Luchangling/WirelessGPSTracker/doc/亮灯规则.jpg

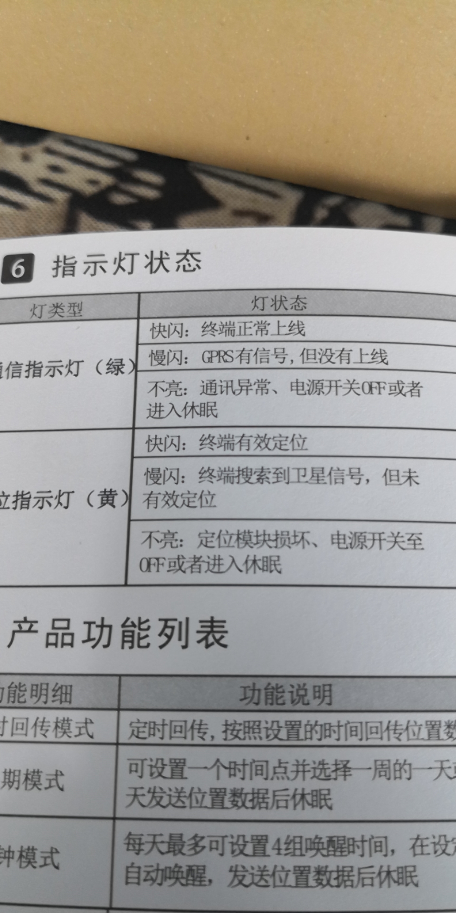
doc/亮灯规则.jpg
