Luchangling/WirelessGPSTracker/mcu/Bsp/src/stm8l15x_it.c

/**
  ******************************************************************************
  * @file    TIM2/TIM2_TRIGLSE/stm8l15x_it.c
  * @author  MCD Application Team
  * @version V1.5.2
  * @date    30-September-2014
  * @brief   Main Interrupt Service Routines.
  *          This file provides template for all peripherals interrupt service routine.
  ******************************************************************************
  * @attention
  *
  * <h2><center>&copy; COPYRIGHT 2014 STMicroelectronics</center></h2>
  *
  * Licensed under MCD-ST Liberty SW License Agreement V2, (the "License");
  * You may not use this file except in compliance with the License.
  * You may obtain a copy of the License at:
  *
  *        http://www.st.com/software_license_agreement_liberty_v2
  *
  * Unless required by applicable law or agreed to in writing, software 
  * distributed under the License is distributed on an "AS IS" BASIS, 
  * WITHOUT WARRANTIES OR CONDITIONS OF ANY KIND, either express or implied.
  * See the License for the specific language governing permissions and
  * limitations under the License.
  *
  ******************************************************************************
  */ 

/* Includes ------------------------------------------------------------------*/
#include "stm8l15x_it.h"
#include "app_ticks_timer.h"
#include "stm8l15x_rtc.h"
#include "main.h"
#include "bsp_comm_uart.h"
#include "bsp_light_sensor.h"
#include "app.h"
#include "bsp.h"
#include "feature_config.h"

/** @addtogroup STM8L15x_StdPeriph_Examples
  * @{
  */

/** @addtogroup TIM2_TRIGLSE
  * @{
  */
/* Private typedef -----------------------------------------------------------*/
/* Private define ------------------------------------------------------------*/
/* Private macro -------------------------------------------------------------*/
/* Private variables ---------------------------------------------------------*/
/* Private function prototypes -----------------------------------------------*/
/* Private functions ---------------------------------------------------------*/
/* Public functions ----------------------------------------------------------*/
static u16 s_exti1 = 0;
#ifdef _COSMIC_
/**
  * @brief Dummy interrupt routine
  * @param  None
  * @retval None
  */
INTERRUPT_HANDLER(NonHandledInterrupt, 0)
{
  /* In order to detect unexpected events during development,
     it is recommended to set a breakpoint on the following instruction.
  */
}
#endif

/**
  * @brief TRAP interrupt routine
  * @param  None
  * @retval None
  */
INTERRUPT_HANDLER_TRAP(TRAP_IRQHandler)
{
  /* In order to detect unexpected events during development,
     it is recommended to set a breakpoint on the following instruction.
  */
}
/**
  * @brief FLASH Interrupt routine.
  * @param  None
  * @retval None
  */
INTERRUPT_HANDLER(FLASH_IRQHandler, 1)
{
  /* In order to detect unexpected events during development,
     it is recommended to set a breakpoint on the following instruction.
  */
}
/**
  * @brief DMA1 channel0 and channel1 Interrupt routine.
  * @param  None
  * @retval None
  */
INTERRUPT_HANDLER(DMA1_CHANNEL0_1_IRQHandler, 2)
{
  /* In order to detect unexpected events during development,
     it is recommended to set a breakpoint on the following instruction.
  */
}
/**
  * @brief DMA1 channel2 and channel3 Interrupt routine.
  * @param  None
  * @retval None
  */
INTERRUPT_HANDLER(DMA1_CHANNEL2_3_IRQHandler, 3)
{
  /* In order to detect unexpected events during development,
     it is recommended to set a breakpoint on the following instruction.
  */
}
/**
  * @brief RTC / CSS_LSE Interrupt routine.
  * @param  None
  * @retval None
  */
INTERRUPT_HANDLER(RTC_CSSLSE_IRQHandler, 4)
{
  /* In order to detect unexpected events during development,
     it is recommended to set a breakpoint on the following instruction.
  */
    RTC_ClearITPendingBit(RTC_IT_ALRA);
    RTC_ClearITPendingBit(RTC_IT_WUT);

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
  * @param  None
  * @retval None
  */
INTERRUPT_HANDLER(USART1_TX_TIM5_UPD_OVF_TRG_BRK_IRQHandler, 27)
{
  /* In order to detect unexpected events during development,
     it is recommended to set a breakpoint on the following instruction.
  */
}

/**
  * @brief USART1 RX / Timer5 Capture/Compare Interrupt routine.
  * @param  None
  * @retval None
  */
INTERRUPT_HANDLER(USART1_RX_TIM5_CC_IRQHandler, 28)
{
  /* In order to detect unexpected events during development,
     it is recommended to set a breakpoint on the following instruction.
  */
	u8 Byte = 0; 

    if(USART_GetITStatus(USART1,USART_IT_RXNE) != RESET)
    {
        Byte = USART_ReceiveData8(USART1) & 0xFF;
        instert_comm_dat_to_queue(Byte);
    }
    else
    {                    
        Byte = USART_ReceiveData8(USART1) & 0xFF;
        //instert_comm_dat_to_queue(Byte);
    }
}

/**
  * @brief I2C1 / SPI2 Interrupt routine.
  * @param  None
  * @retval None
  */
INTERRUPT_HANDLER(I2C1_SPI2_IRQHandler, 29)
{
  /* In order to detect unexpected events during development,
     it is recommended to set a breakpoint on the following instruction.
  */
}


/**
  * @}
  */
/************************ (C) COPYRIGHT STMicroelectronics *****END OF FILE****/
  
