Luchangling/WirelessGPSTracker/mtk/src/nmea_protocol.c

/**
 * Copyright @ Goome Technologies Co., Ltd. 2009-2019. All rights reserved.
 * File name:        nmea.h
 * Author:           王志华       
 * Version:          1.0
 * Date:             2019-03-19
 * Description:      GPS标准协议NMEA-0183实现
 * Others:           
 * Function List:    
    1. 
    
 * History: 
    1. Date:         2019-03-19
       Author:       王志华
       Modification: 创建初始版本
    2. Date: 		 
	   Author:		 
	   Modification: 

 */

#include <stdlib.h>
#include <string.h>
#include <ctype.h>
#include <stdarg.h>
#include <time.h>
#include <stdint.h>
#include <math.h>
#include <gm_stdlib.h>
#include "utility.h"
#include "nmea_protocol.h"
#include "log_service.h"

#define MAX_TYPE_LEN 12

// AGPS信息（位置,时间,频率）
typedef struct  
{
	double lat;
	double lng;
	double alt;
	double tow;
	float df;
	float pos_acc;
	float t_acc; 
	float f_acc; 
	U32	res;
	U16 wn;
	U8 	time_source;
	U8	flags;// BIT0:位置有效标志 BIT1:时间有效标志
} ATAidInfo;


static S32 hex2int(char c);

static U8 nmea_checksum(const char* p_sentence);

static bool nmea_check(const char* p_sentence, bool strict);

static bool nmea_isfield(char c);

static bool nmea_scan(const char* p_sentence, const char *format, ...);

static bool nmea_create_td_sentence(const U16 cmd,const U8* p_data,const U16 data_len, U8* p_sentence, U8* p_len);


static S32 hex2int(char c)
{
    if (c >= '0' && c <= '9')
    {
        return c - '0';
    }
    if (c >= 'A' && c <= 'F')
	{
        return c - 'A' + 10;
    }
    if (c >= 'a' && c <= 'f')
    {
        return c - 'a' + 10;
    }
    return -1;
}



/**
 * Function:   检查语句有效性和校验和
 * Description:不检查语句完整性
 * Input:	   无
 * Output:	   无
 * Return:	   true——有效；false——无效
 * Others:	   
 */
static bool nmea_check(const char* p_sentence, bool strict)
{
    U8 checksum = 0;
	S32 upper = 0;
	S32 lower = 0;
	S32 expected = 0;
	const char* org_sentence = p_sentence;

    // 语句长度限制
    if (strlen(p_sentence) > SENTENCE_MAX_LENGTH + 3)
    {
    	
        return false;
    }

    // 有效的语句应该以'$'开头
    if (*p_sentence++ != '$')
    {
    	LOG(WARN,"It is not begin with $!");
        return false;
    }

    while (*p_sentence && *p_sentence != '*' && util_isprint((U8)*p_sentence))
    {
        checksum ^= *p_sentence++;
    }

	// 有校验和
    if (*p_sentence == '*') 
	{
        p_sentence++;
		
        upper = hex2int(*p_sentence++);
        if (upper == -1)
        {
        	LOG(WARN,"upper is -1");
            return false;
        }
		
        lower = hex2int(*p_sentence++);
        if (lower == -1)
        {
        	LOG(WARN,"lower is -1");
            return false;
        }
		
        expected = upper << 4 | lower;
        if (checksum != expected)
        {
        	LOG(WARN, "checksum=%d,expected=%d", checksum,expected);
            return false;
        }
    } 
	else if (strict) 
	{
        // 严格模式下没有校验和的数据是无效的
        LOG(WARN,"It has not checksum:%s",org_sentence);
        return false;
    }

    // 最后一定要是换行
    if (strict && *p_sentence && GM_strcmp(p_sentence, "\n") && GM_strcmp(p_sentence, "\r\n"))
    {
    	LOG(WARN," It has not end flag:%s",org_sentence);
        return false;
    }

    return true;
}

static bool nmea_isfield(char c) 
{
    return util_isprint((U8)c) && c != ',' && c != '*';
}

/**
 * Function:   从语句中提取变量
 * Description:
 * Input:	   p_sentence:语句；format——格式；
 * Output:	   ...——变量
 * Return:	   true——成功；false——失败
 * Others:	   类似于scanf的处理方式,支持下面几种格式:
               c - single character (char*)
               d - direction, returned as 1/-1, default 0 (S32*)
               f - fractional, returned as value + scale (S32*, S32*)
               i - decimal, default zero (S32*)
               s - string (char*)
               t - talker identifier and type (char*)
               T - date/time stamp (S32*, S32*, S32*)              
 */         
static bool nmea_scan(const char* p_sentence, const char* p_format, ...)

{
    bool result = false;
    bool optional = false;
	const char* p_field = p_sentence;
	char type = 0;
	char value_8 = 0;
	S32 value_32 = 0;
	S32 sign_32 = 0;
    S32 scale_32 = 0;
	S32 digit_32 = 0;
	char* p_buf = NULL;
	U8 index = 0;
	S32 d = 0;
	S32 m = 0;
	S32 y = 0;
	char dArr[3] = {0};
	char mArr[3] = {0};
	char yArr[3] = {0};
	char hArr[3] = {0};
	char iArr[3] = {0};
	char sArr[3] = {0};
	NMEAFloat fraction = {0};
	NMEATime* p_time = NULL;
	S32 h = -1;
	S32 i = -1;
	S32 s = -1;
	S32 u = -1;

	
    va_list ap;
    va_start(ap, p_format);

    while (*p_format) 
	{
        type = *p_format++;

        if (type == ';') 
		{
            // 后面所有的域都是可选的
            optional = true;
            continue;
        }

        if (!p_field && !optional) 
		{
            goto parse_error;
        }

        switch (type) 
		{
			// Single character field(char)
            case 'c': 
			{
                value_8 = '\0';
                if (p_field && nmea_isfield(*p_field))
                {
                    value_8 = *p_field;
                }

                *va_arg(ap, char*) = value_8;
            } 
			break;
			// Single character direction field(S32)
            case 'd': 
			{
                value_32 = 0;

                if (p_field && nmea_isfield(*p_field)) 
				{
                    switch (*p_field) 
					{
                        case 'N':
                        case 'E':
                            value_32 = 1;
                            break;
                        case 'S':
                        case 'W':
                            value_32 = -1;
                            break;
                        default:
                            goto parse_error;
                    }
                }

                *va_arg(ap, S32*) = value_32;
            } 
			break;

			// Fractional value with scale (NMEAFloat).
            case 'f': 
			{
                sign_32 = 0;
                value_32 = -1;
                scale_32 = 0;
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
